Ttreintaysiete/ardcore/software/sketches/fac_drums_8552/pitch_table.c

#include "pitch_table.h"

PROGMEM prog_uint32_t pitch_table[2048] = {
	32768, 32812, 32857, 32901, 32946, 32991, 33035, 33080, 33125, 33170, 33215, 33260, 33305, 33350, 33395, 33440, 
	33486, 33531, 33576, 33622, 33667, 33713, 33759, 33804, 33850, 33896, 33942, 33988, 34034, 34080, 34126, 34172, 
	34219, 34265, 34312, 34358, 34405, 34451, 34498, 34545, 34591, 34638, 34685, 34732, 34779, 34826, 34874, 34921, 
	34968, 35015, 35063, 35110, 35158, 35206, 35253, 35301, 35349, 35397, 35445, 35493, 35541, 35589, 35637, 35685, 
	35734, 35782, 35831, 35879, 35928, 35976, 36025, 36074, 36123, 36172, 36221, 36270, 36319, 36368, 36417, 36467, 
	36516, 36566, 36615, 36665, 36715, 36764, 36814, 36864, 36914, 36964, 37014, 37064, 37114, 37165, 37215, 37265, 
	37316, 37366, 37417, 37468, 37518, 37569, 37620, 37671, 37722, 37773, 37824, 37876, 37927, 37978, 38030, 38081, 
	38133, 38185, 38236, 38288, 38340, 38392, 38444, 38496, 38548, 38600, 38653, 38705, 38757, 38810, 38863, 38915, 
	38968, 39021, 39074, 39127, 39180, 39233, 39286, 39339, 39392, 39446, 39499, 39553, 39606, 39660, 39714, 39767, 
	39821, 39875, 39929, 39983, 40037, 40092, 40146, 40200, 40255, 40309, 40364, 40419, 40473, 40528, 40583, 40638, 
	40693, 40748, 40804, 40859, 40914, 40970, 41025, 41081, 41136, 41192, 41248, 41304, 41360, 41416, 41472, 41528, 
	41584, 41641, 41697, 41753, 41810, 41867, 41923, 41980, 42037, 42094, 42151, 42208, 42265, 42323, 42380, 42437, 
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
	74632, 74733, 74834, 74935, 75037, 75139, 75240, 75342, 75444, 75547, 75649, 75751, 75854, 75957, 76060, 76163, 
	76266, 76369, 76473, 76576, 76680, 76784, 76888, 76992, 77096, 77201, 77305, 77410, 77515, 77620, 77725, 77830, 
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
};
