Ttreintaysiete/ardcore/software/sketches/fac_drums_8552/sample0.c

#include "sample0.h"

prog_uchar sample0_data[sample0_size] = {
	134, 122, 175, 216, 53, 137, 172, 89, 180, 91, 102, 141, 160, 138, 86, 157, 
	101, 152, 125, 105, 200, 39, 177, 182, 2, 158, 191, 171, 97, 120, 173, 78, 
	101, 140, 58, 129, 231, 158, 38, 151, 216, 29, 86, 255, 71, 95, 161, 104, 
	142, 161, 122, 110, 142, 107, 117, 114, 160, 67, 141, 181, 83, 135, 162, 109, 
	37, 181, 222, 57, 141, 126, 115, 151, 170, 93, 125, 150, 78, 179, 108, 161, 
	114, 114, 158, 153, 139, 99, 146, 118, 160, 86, 146, 144, 132, 158, 114, 126, 
	125, 113, 124, 163, 98, 163, 120, 89, 139, 130, 150, 83, 194, 96, 163, 72, 
	149, 154, 106, 155, 90, 164, 113, 135, 144, 84, 173, 107, 111, 126, 145, 118, 
	128, 145, 136, 131, 117, 136, 133, 129, 120, 134, 111, 156, 128, 142, 102, 128, 
	115, 125, 139, 134, 163, 101, 135, 119, 156, 112, 120, 101, 167, 132, 129, 150, 
	87, 167, 101, 120, 155, 130, 105, 154, 130, 112, 148, 118, 118, 110, 172, 103, 
	149, 148, 99, 132, 113, 135, 121, 115, 138, 128, 140, 138, 88, 140, 159, 117, 
	105, 160, 130, 137, 102, 121, 176, 121, 128, 104, 148, 143, 114, 106, 166, 107, 
	164, 134, 84, 153, 136, 123, 162, 98, 129, 139, 135, 130, 119, 146, 137, 131, 
	90, 162, 118, 139, 113, 129, 134, 113, 151, 125, 111, 142, 142, 142, 112, 128, 
	145, 152, 107, 109, 135, 161, 118, 141, 98, 139, 131, 136, 118, 104, 167, 112, 
	130, 118, 83, 202, 127, 98, 154, 116, 143, 107, 128, 153, 164, 71, 128, 163, 
	113, 117, 141, 120, 128, 139, 147, 80, 150, 146, 107, 143, 84, 153, 152, 123, 
	138, 136, 112, 117, 154, 124, 143, 136, 89, 176, 114, 87, 168, 137, 104, 134, 
	155, 103, 148, 125, 89, 161, 129, 101, 159, 122, 126, 137, 125, 135, 130, 136, 
	126, 119, 132, 137, 117, 128, 149, 116, 129, 160, 82, 175, 149, 94, 136, 148, 
	105, 137, 132, 122, 130, 136, 118, 126, 165, 91, 147, 134, 137, 131, 82, 172, 
	116, 147, 101, 162, 114, 134, 123, 128, 162, 106, 123, 129, 129, 166, 93, 109, 
	175, 92, 132, 152, 122, 129, 133, 135, 97, 155, 118, 139, 163, 62, 150, 134, 
	127, 139, 129, 128, 134, 98, 137, 167, 110, 139, 111, 123, 150, 132, 149, 95, 
	140, 128, 132, 124, 124, 162, 113, 121, 140, 132, 117, 136, 148, 114, 97, 168, 
	130, 138, 122, 132, 109, 137, 151, 80, 175, 112, 121, 148, 113, 155, 128, 117, 
	128, 130, 139, 109, 151, 128, 153, 94, 127, 149, 114, 157, 103, 152, 96, 132, 
	167, 93, 148, 119, 122, 158, 109, 128, 124, 172, 101, 126, 136, 110, 159, 134, 
	113, 100, 178, 126, 90, 178, 120, 109, 140, 114, 156, 136, 130, 122, 128, 147, 
	113, 138, 128, 143, 117, 130, 129, 119, 149, 110, 141, 128, 113, 136, 153, 126, 
	112, 131, 138, 120, 138, 138, 125, 122, 127, 124, 150, 126, 140, 108, 133, 129, 
	117, 143, 137, 114, 116, 167, 104, 123, 148, 121, 121, 131, 148, 117, 130, 117, 
	132, 162, 106, 108, 149, 131, 124, 125, 124, 129, 138, 131, 134, 133, 100, 140, 
	131, 148, 155, 94, 143, 134, 125, 133, 134, 120, 137, 109, 127, 153, 122, 113, 
	171, 80, 154, 126, 103, 143, 152, 115, 137, 115, 151, 117, 123, 138, 126, 151, 
	113, 124, 145, 139, 118, 127, 115, 150, 123, 139, 118, 135, 127, 133, 128, 132, 
	128, 135, 131, 109, 154, 116, 140, 125, 147, 83, 147, 120, 152, 108, 111, 141, 
	142, 128, 126, 123, 136, 134, 132, 110, 160, 132, 133, 116, 128, 137, 131, 146, 
	109, 141, 129, 118, 114, 147, 148, 125, 116, 133, 112, 145, 141, 140, 117, 94, 
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
};
