Ttreintaysiete/ardcore/software/sketches/fac_drums_8552/sample1.c

#include "sample1.h"

prog_uchar sample1_data[sample1_size] = {
	128, 132, 137, 110, 105, 174, 113, 117, 152, 100, 147, 127, 111, 162, 96, 142, 
	130, 119, 151, 124, 131, 118, 143, 144, 140, 125, 143, 158, 109, 129, 187, 125, 
	83, 157, 140, 121, 150, 171, 121, 149, 122, 133, 139, 129, 121, 80, 144, 91, 
	116, 130, 101, 118, 81, 143, 169, 77, 135, 124, 87, 134, 148, 83, 166, 108, 
	128, 202, 84, 122, 149, 151, 139, 119, 140, 172, 102, 179, 85, 150, 98, 174, 
	87, 141, 126, 132, 137, 122, 131, 134, 138, 106, 67, 175, 109, 149, 110, 112, 
	160, 102, 128, 116, 187, 105, 107, 211, 94, 151, 136, 173, 141, 98, 162, 151, 
	157, 164, 83, 181, 128, 103, 176, 80, 183, 96, 118, 165, 93, 134, 146, 125, 
	113, 106, 178, 61, 144, 91, 187, 146, 44, 224, 43, 163, 137, 100, 147, 90, 
	87, 160, 99, 142, 128, 95, 130, 71, 116, 216, 88, 100, 144, 68, 147, 104, 
	119, 119, 92, 186, 106, 114, 198, 71, 199, 132, 81, 231, 65, 225, 123, 140, 
	191, 71, 178, 108, 153, 185, 145, 113, 162, 65, 226, 110, 112, 123, 136, 141, 
	103, 151, 84, 146, 141, 97, 118, 95, 126, 124, 122, 121, 63, 149, 114, 119, 
	93, 177, 78, 145, 127, 75, 186, 31, 184, 92, 146, 162, 95, 193, 121, 112, 
	181, 130, 160, 126, 103, 227, 78, 179, 147, 97, 132, 151, 161, 119, 124, 108, 
	150, 162, 87, 140, 121, 145, 142, 92, 156, 111, 116, 149, 89, 95, 186, 81, 
	134, 124, 104, 182, 50, 198, 60, 167, 134, 107, 141, 135, 102, 131, 137, 148, 
	80, 166, 146, 129, 136, 143, 153, 129, 152, 151, 97, 125, 152, 111, 88, 196, 
	89, 79, 178, 67, 154, 180, 48, 170, 69, 164, 114, 92, 186, 41, 196, 109, 
	115, 205, 72, 151, 121, 113, 200, 63, 200, 125, 148, 109, 164, 128, 99, 186, 
	181, 116, 86, 166, 96, 140, 127, 122, 172, 61, 135, 166, 84, 116, 113, 104, 
	118, 128, 119, 123, 149, 127, 79, 198, 136, 117, 153, 125, 144, 146, 138, 83, 
	177, 126, 120, 178, 55, 141, 146, 80, 129, 148, 110, 112, 137, 132, 131, 115, 
	113, 125, 162, 101, 117, 161, 78, 221, 99, 135, 159, 100, 219, 87, 176, 140, 
	56, 216, 123, 105, 200, 94, 138, 171, 79, 194, 100, 148, 132, 95, 148, 141, 
	82, 147, 92, 107, 152, 79, 158, 60, 137, 157, 42, 170, 96, 141, 124, 133, 
	156, 120, 102, 157, 112, 132, 143, 148, 145, 149, 128, 152, 112, 172, 128, 69, 
	255, 22, 172, 130, 162, 108, 128, 128, 106, 155, 104, 119, 165, 65, 132, 152, 
	106, 124, 151, 168, 39, 178, 85, 155, 150, 118, 69, 187, 96, 162, 150, 89, 
	131, 135, 136, 134, 125, 115, 140, 108, 154, 115, 142, 128, 94, 212, 43, 153, 
	170, 78, 219, 40, 216, 124, 101, 183, 84, 153, 134, 120, 138, 106, 137, 150, 
	88, 179, 149, 85, 204, 76, 126, 152, 140, 127, 104, 126, 121, 143, 134, 107, 
	153, 115, 112, 164, 86, 111, 133, 128, 111, 137, 159, 81, 155, 139, 92, 172, 
	105, 127, 163, 97, 154, 164, 116, 146, 135, 124, 204, 80, 151, 159, 76, 215, 
	80, 135, 151, 88, 166, 101, 119, 141, 109, 173, 82, 133, 131, 110, 129, 117, 
	120, 147, 117, 128, 108, 129, 142, 113, 123, 135, 131, 132, 156, 100, 153, 106, 
	119, 149, 133, 138, 153, 120, 165, 136, 137, 124, 119, 171, 152, 98, 141, 146, 
	122, 130, 149, 116, 138, 120, 145, 95, 120, 151, 98, 123, 121, 118, 142, 115, 
	116, 132, 101, 160, 73, 169, 118, 59, 201, 123, 101, 158, 128, 168, 97, 175, 
	104, 147, 123, 128, 164, 109, 136, 156, 117, 138, 110, 186, 115, 118, 132, 117, 
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
};
