Ttreintaysiete/ardcore/software/sketches/fac_drums_8552/sample2.c

#include "sample2.h"

prog_uchar sample2_data[sample2_size] = {
	129, 128, 124, 126, 124, 124, 124, 123, 114, 104, 98, 108, 86, 91, 92, 68, 
	67, 27, 39, 87, 115, 79, 49, 49, 90, 96, 79, 84, 108, 75, 112, 110, 
	101, 132, 123, 129, 147, 155, 138, 171, 179, 157, 187, 192, 200, 193, 207, 231, 
	213, 250, 232, 246, 252, 245, 251, 248, 252, 251, 252, 252, 253, 252, 253, 252, 
	254, 253, 255, 253, 255, 254, 255, 254, 249, 250, 249, 232, 230, 234, 208, 220, 
	198, 203, 181, 182, 167, 156, 161, 129, 134, 119, 118, 90, 98, 94, 59, 54, 
	65, 51, 26, 32, 27, 18, 18, 21, 19, 19, 18, 17, 17, 17, 16, 16, 
	16, 15, 15, 16, 14, 15, 14, 14, 13, 13, 12, 14, 11, 12, 11, 12, 
	10, 10, 10, 10, 9, 9, 8, 9, 8, 7, 8, 7, 8, 14, 17, 36, 
	39, 39, 71, 58, 70, 99, 81, 128, 97, 135, 151, 134, 161, 172, 174, 183, 
	201, 197, 214, 214, 234, 226, 236, 239, 235, 237, 236, 238, 237, 239, 237, 239, 
	239, 239, 239, 239, 240, 241, 240, 241, 240, 242, 241, 241, 243, 243, 242, 244, 
	242, 245, 243, 245, 244, 246, 245, 245, 247, 246, 247, 245, 241, 239, 231, 218, 
	211, 215, 191, 193, 183, 171, 170, 144, 159, 145, 125, 122, 124, 109, 97, 100, 
	91, 76, 79, 57, 72, 55, 38, 58, 32, 33, 38, 20, 34, 21, 21, 23, 
	23, 20, 23, 20, 22, 20, 21, 20, 20, 19, 20, 19, 18, 19, 19, 17, 
	18, 18, 17, 17, 17, 15, 17, 15, 15, 16, 15, 14, 15, 13, 15, 12, 
	16, 26, 22, 26, 37, 31, 41, 50, 35, 60, 51, 66, 63, 70, 76, 82, 
	82, 89, 106, 95, 101, 126, 118, 128, 133, 133, 155, 142, 165, 158, 178, 173, 
	180, 190, 194, 198, 204, 210, 211, 221, 225, 225, 223, 226, 226, 227, 225, 228, 
	227, 227, 228, 229, 228, 228, 230, 228, 230, 230, 230, 231, 231, 230, 233, 231, 
	232, 232, 233, 233, 233, 233, 234, 234, 234, 235, 235, 236, 235, 236, 236, 237, 
	237, 236, 239, 236, 239, 238, 239, 239, 239, 239, 241, 232, 237, 232, 221, 230, 
	220, 213, 213, 212, 203, 200, 191, 194, 190, 178, 176, 178, 160, 166, 160, 148, 
	149, 145, 129, 135, 132, 122, 121, 120, 117, 113, 109, 105, 101, 94, 90, 85, 
	80, 74, 71, 64, 62, 55, 52, 48, 46, 42, 42, 40, 40, 39, 39, 39, 
	38, 39, 39, 38, 37, 38, 38, 36, 37, 36, 36, 35, 36, 35, 34, 35, 
	34, 33, 34, 33, 32, 33, 31, 31, 33, 29, 31, 30, 30, 29, 30, 28, 
	29, 28, 28, 27, 28, 26, 28, 37, 48, 46, 48, 46, 46, 46, 47, 47, 
	46, 49, 49, 51, 55, 56, 58, 61, 64, 66, 68, 70, 74, 75, 78, 80, 
	83, 85, 89, 89, 94, 94, 98, 101, 103, 105, 108, 111, 113, 115, 118, 121, 
	123, 126, 128, 130, 132, 136, 137, 139, 144, 144, 148, 149, 154, 154, 158, 159, 
	162, 165, 166, 168, 172, 173, 176, 178, 180, 182, 185, 186, 189, 190, 193, 195, 
	195, 199, 199, 200, 202, 200, 203, 202, 202, 203, 203, 204, 203, 204, 204, 205, 
	204, 205, 206, 206, 205, 208, 206, 207, 208, 208, 207, 209, 209, 209, 210, 209, 
	210, 210, 211, 211, 211, 213, 211, 212, 213, 213, 213, 214, 213, 214, 215, 214, 
	215, 215, 216, 216, 216, 216, 216, 217, 216, 218, 215, 217, 214, 213, 212, 211, 
	208, 206, 205, 203, 201, 198, 197, 193, 192, 190, 187, 185, 181, 181, 176, 175, 
	172, 170, 166, 165, 161, 159, 156, 155, 149, 149, 145, 143, 140, 138, 135, 131, 
	131, 127, 126, 121, 120, 118, 114, 113, 110, 108, 106, 102, 102, 97, 97, 95, 
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
};
