Ttreintaysiete/ardcore/software/sketches/fac_drums_8552/sample3.c

#include "sample3.h"

prog_uchar sample3_data[sample3_size] = {
	128, 123, 85, 126, 147, 103, 193, 103, 102, 70, 88, 121, 165, 128, 114, 126, 
	58, 128, 134, 78, 163, 149, 20, 91, 79, 52, 70, 40, 91, 94, 67, 79, 
	130, 135, 90, 91, 92, 96, 75, 66, 79, 45, 67, 53, 28, 85, 114, 75, 
	79, 88, 83, 91, 119, 128, 118, 92, 83, 75, 58, 97, 128, 137, 104, 92, 
	73, 78, 106, 137, 170, 145, 59, 103, 160, 195, 193, 174, 133, 103, 157, 196, 
	144, 128, 154, 138, 93, 101, 110, 136, 194, 230, 190, 128, 137, 154, 127, 150, 
	170, 166, 169, 176, 179, 175, 197, 244, 237, 180, 139, 157, 220, 255, 248, 231, 
	214, 189, 162, 152, 199, 248, 235, 227, 217, 203, 204, 201, 190, 176, 180, 184, 
	190, 205, 210, 220, 232, 224, 210, 194, 187, 192, 189, 191, 197, 189, 188, 206, 
	208, 213, 227, 212, 191, 176, 171, 172, 177, 176, 194, 205, 194, 175, 163, 164, 
	175, 175, 168, 160, 149, 135, 128, 134, 134, 137, 151, 149, 133, 149, 148, 120, 
	97, 108, 128, 141, 144, 145, 155, 147, 113, 76, 76, 89, 79, 64, 54, 56, 
	61, 64, 61, 49, 27, 38, 55, 59, 66, 63, 61, 66, 70, 64, 52, 46, 
	59, 67, 49, 38, 41, 50, 54, 56, 46, 21, 13, 31, 34, 21, 40, 41, 
	23, 15, 9, 9, 9, 12, 10, 13, 33, 48, 48, 42, 38, 38, 32, 29, 
	27, 43, 75, 85, 61, 67, 84, 66, 57, 83, 97, 98, 93, 83, 72, 53, 
	48, 66, 86, 85, 73, 64, 70, 82, 89, 94, 89, 82, 76, 79, 76, 71, 
	78, 84, 89, 90, 98, 104, 105, 102, 92, 85, 84, 90, 97, 95, 97, 95, 
	96, 102, 115, 115, 101, 100, 117, 108, 96, 100, 108, 107, 100, 95, 94, 89, 
	80, 73, 78, 91, 98, 92, 83, 77, 81, 83, 82, 69, 75, 97, 98, 75, 
	75, 91, 88, 76, 68, 72, 82, 93, 92, 77, 52, 41, 43, 51, 57, 57, 
	55, 52, 56, 62, 68, 61, 61, 71, 77, 70, 71, 76, 82, 84, 87, 87, 
	92, 92, 94, 97, 105, 110, 116, 117, 114, 109, 108, 113, 114, 102, 99, 108, 
	122, 126, 133, 139, 145, 147, 152, 153, 154, 145, 139, 137, 141, 148, 151, 154, 
	161, 169, 174, 164, 161, 175, 187, 182, 180, 184, 194, 201, 202, 206, 207, 214, 
	222, 224, 222, 218, 217, 218, 220, 220, 221, 214, 212, 221, 228, 226, 224, 233, 
	240, 243, 243, 241, 238, 238, 237, 236, 238, 238, 237, 237, 239, 240, 245, 246, 
	246, 243, 242, 246, 246, 246, 241, 238, 241, 239, 239, 234, 229, 226, 226, 229, 
	233, 233, 230, 228, 225, 224, 219, 215, 215, 222, 228, 216, 204, 206, 207, 207, 
	200, 196, 191, 189, 183, 180, 179, 178, 182, 182, 179, 176, 173, 171, 172, 170, 
	159, 150, 148, 150, 147, 137, 133, 129, 129, 128, 127, 123, 118, 116, 111, 108, 
	105, 102, 99, 97, 96, 96, 97, 92, 89, 86, 85, 83, 78, 73, 70, 68, 
	75, 78, 77, 71, 68, 69, 68, 69, 68, 70, 72, 69, 61, 52, 57, 64, 
	66, 59, 53, 52, 53, 54, 58, 58, 61, 59, 55, 53, 51, 50, 53, 52, 
	53, 49, 50, 58, 67, 69, 62, 62, 63, 65, 66, 64, 64, 62, 64, 64, 
	66, 69, 68, 71, 72, 71, 75, 73, 78, 75, 78, 78, 80, 79, 76, 75, 
	77, 78, 81, 83, 86, 91, 93, 96, 96, 96, 96, 95, 93, 91, 92, 98, 
	103, 101, 94, 88, 92, 97, 100, 101, 101, 99, 99, 101, 102, 106, 108, 110, 
	109, 108, 110, 113, 113, 108, 102, 102, 105, 110, 112, 111, 111, 113, 112, 116, 
	114, 117, 115, 117, 116, 119, 118, 118, 120, 118, 120, 120, 120, 119, 121, 123, 
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
};
