Ttreintaysiete/ardcore/software/sketches/fac_drums_8552/sample4.c

#include "sample4.h"

prog_uchar sample4_data[sample4_size] = {
	129, 127, 91, 88, 87, 90, 86, 84, 88, 99, 68, 66, 72, 94, 127, 57, 
	24, 126, 105, 31, 111, 156, 141, 165, 166, 55, 134, 127, 204, 187, 139, 169, 
	105, 157, 201, 189, 206, 255, 169, 70, 142, 232, 219, 218, 204, 149, 172, 235, 
	215, 73, 158, 245, 183, 163, 189, 190, 188, 216, 188, 57, 108, 103, 195, 225, 
	79, 99, 143, 111, 176, 204, 25, 72, 119, 203, 147, 2, 53, 118, 125, 121, 
	85, 101, 79, 50, 83, 94, 85, 148, 148, 2, 79, 201, 70, 24, 110, 113, 
	139, 108, 41, 80, 104, 109, 106, 102, 103, 127, 85, 99, 105, 119, 127, 211, 
	99, 28, 85, 137, 198, 137, 117, 136, 143, 146, 133, 155, 162, 109, 139, 162, 
	237, 142, 29, 95, 195, 205, 213, 225, 107, 97, 185, 198, 140, 158, 193, 210, 
	131, 164, 183, 250, 129, 140, 165, 100, 129, 196, 196, 205, 147, 139, 156, 166, 
	154, 135, 133, 160, 150, 101, 127, 180, 162, 23, 123, 140, 135, 142, 116, 22, 
	65, 123, 137, 115, 110, 105, 90, 62, 138, 88, 48, 79, 167, 59, 99, 84, 
	37, 137, 154, 45, 138, 65, 45, 124, 101, 115, 118, 114, 154, 96, 101, 78, 
	133, 153, 36, 114, 144, 161, 139, 137, 131, 135, 152, 173, 93, 110, 159, 143, 
	144, 156, 174, 205, 58, 117, 154, 223, 193, 116, 93, 113, 182, 201, 158, 163, 
	226, 126, 105, 133, 135, 184, 203, 191, 114, 174, 143, 109, 162, 170, 165, 150, 
	147, 135, 153, 149, 182, 112, 83, 132, 187, 151, 97, 98, 83, 154, 138, 118, 
	120, 136, 111, 99, 114, 137, 91, 59, 94, 119, 101, 117, 141, 96, 69, 47, 
	90, 127, 126, 102, 102, 103, 90, 110, 86, 112, 120, 141, 84, 34, 114, 129, 
	132, 123, 121, 119, 137, 106, 118, 122, 123, 147, 168, 145, 53, 105, 165, 203, 
	151, 66, 130, 162, 174, 174, 189, 119, 127, 130, 126, 165, 169, 176, 185, 101, 
	129, 167, 164, 200, 189, 96, 114, 174, 145, 121, 171, 168, 161, 161, 134, 126, 
	154, 164, 161, 126, 86, 142, 138, 152, 142, 138, 138, 174, 84, 140, 91, 92, 
	148, 154, 129, 121, 72, 84, 120, 164, 136, 93, 106, 88, 112, 124, 127, 64, 
	110, 115, 117, 119, 154, 70, 63, 104, 159, 74, 98, 114, 132, 104, 133, 123, 
	78, 89, 150, 111, 139, 98, 83, 120, 160, 140, 139, 130, 71, 116, 171, 166, 
	100, 128, 141, 151, 162, 123, 147, 168, 93, 141, 153, 186, 129, 131, 147, 159, 
	157, 191, 131, 100, 189, 129, 113, 178, 166, 127, 152, 153, 160, 177, 113, 153, 
	147, 99, 128, 156, 164, 145, 133, 131, 133, 136, 133, 136, 136, 120, 144, 155, 
	68, 98, 134, 143, 127, 147, 151, 57, 95, 126, 134, 128, 118, 143, 79, 89, 
	122, 131, 104, 130, 109, 92, 99, 113, 132, 110, 115, 128, 125, 85, 103, 96, 
	106, 133, 130, 139, 110, 105, 134, 151, 73, 124, 153, 104, 101, 136, 138, 172, 
	128, 89, 125, 148, 150, 155, 118, 110, 142, 150, 144, 136, 139, 141, 141, 142, 
	139, 173, 145, 89, 129, 152, 157, 149, 145, 141, 143, 142, 173, 120, 106, 146, 
	146, 157, 143, 138, 132, 127, 130, 164, 131, 109, 154, 109, 125, 138, 141, 136, 
	160, 105, 94, 130, 133, 143, 122, 134, 116, 121, 99, 113, 139, 148, 96, 117, 
	127, 114, 111, 109, 126, 127, 127, 117, 114, 140, 120, 95, 99, 125, 139, 99, 
	131, 121, 129, 136, 95, 107, 128, 153, 121, 96, 128, 129, 132, 126, 133, 123, 
	151, 129, 95, 128, 138, 140, 136, 134, 133, 138, 133, 133, 133, 143, 158, 110, 
	122, 140, 155, 140, 134, 142, 137, 141, 154, 156, 107, 148, 135, 130, 151, 128, 
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
};
