Ttreintaysiete/ardcore/software/sketches/fac_drums_8552/sample5.c

#include "sample5.h"

prog_uchar sample5_data[sample5_size] = {
	127, 135, 141, 129, 77, 230, 205, 164, 182, 155, 219, 187, 166, 194, 165, 152, 
	185, 158, 155, 160, 140, 151, 117, 137, 120, 51, 122, 100, 46, 67, 44, 42, 
	21, 29, 21, 18, 12, 48, 19, 32, 75, 2, 64, 77, 23, 63, 70, 91, 
	89, 80, 118, 123, 112, 121, 194, 139, 143, 199, 201, 167, 238, 184, 193, 245, 
	208, 212, 187, 254, 193, 217, 207, 205, 239, 153, 180, 211, 142, 145, 150, 166, 
	124, 136, 133, 102, 94, 115, 86, 131, 57, 74, 142, 56, 115, 83, 61, 145, 
	66, 89, 31, 120, 107, 71, 120, 56, 97, 96, 61, 116, 67, 117, 121, 71, 
	88, 91, 110, 98, 84, 96, 121, 62, 123, 113, 83, 145, 98, 117, 134, 117, 
	128, 139, 146, 152, 107, 165, 165, 150, 175, 127, 214, 159, 141, 196, 163, 150, 
	216, 160, 163, 190, 195, 192, 216, 205, 166, 217, 231, 190, 225, 247, 239, 198, 
	255, 231, 226, 223, 209, 248, 219, 201, 236, 230, 186, 218, 187, 198, 205, 175, 
	171, 171, 173, 173, 125, 155, 163, 118, 127, 91, 157, 125, 92, 102, 101, 118, 
	75, 84, 98, 60, 51, 86, 48, 78, 31, 32, 89, 28, 35, 61, 39, 42, 
	22, 78, 16, 68, 40, 49, 49, 81, 49, 70, 77, 85, 86, 84, 94, 97, 
	108, 104, 113, 112, 119, 132, 123, 143, 145, 175, 143, 201, 176, 160, 206, 186, 
	215, 173, 210, 224, 189, 235, 184, 199, 239, 171, 231, 228, 186, 201, 203, 204, 
	178, 210, 205, 153, 195, 182, 159, 171, 141, 158, 178, 145, 141, 137, 142, 146, 
	96, 116, 163, 91, 121, 128, 94, 87, 123, 75, 110, 67, 79, 104, 41, 98, 
	71, 42, 57, 91, 67, 44, 53, 92, 71, 48, 67, 50, 79, 59, 63, 61, 
	65, 67, 55, 60, 87, 88, 48, 74, 136, 47, 89, 128, 54, 115, 90, 129, 
	110, 114, 113, 117, 136, 110, 140, 135, 145, 169, 139, 155, 147, 167, 190, 136, 
	193, 201, 196, 159, 161, 213, 232, 162, 216, 220, 163, 213, 202, 229, 176, 197, 
	235, 187, 138, 195, 225, 151, 183, 223, 145, 191, 221, 128, 214, 195, 102, 187, 
	149, 158, 148, 116, 167, 109, 112, 142, 48, 131, 97, 113, 126, 90, 74, 93, 
	98, 89, 86, 119, 84, 87, 99, 91, 84, 53, 99, 112, 91, 43, 108, 102, 
	101, 84, 93, 66, 107, 75, 121, 119, 47, 112, 112, 76, 119, 79, 79, 123, 
	92, 115, 85, 97, 124, 61, 86, 134, 82, 76, 98, 149, 65, 113, 121, 96, 
	67, 99, 132, 84, 126, 88, 104, 159, 77, 97, 153, 92, 119, 111, 123, 128, 
	109, 163, 132, 111, 154, 114, 127, 163, 129, 156, 147, 133, 114, 174, 149, 155, 
	128, 159, 184, 130, 144, 152, 144, 158, 135, 153, 178, 133, 172, 171, 130, 190, 
	160, 170, 159, 150, 160, 178, 167, 150, 207, 142, 163, 203, 139, 178, 191, 130, 
	178, 167, 157, 183, 149, 147, 168, 160, 138, 151, 152, 131, 150, 142, 127, 131, 
	142, 139, 101, 128, 118, 117, 135, 95, 106, 117, 122, 67, 96, 151, 60, 124, 
	121, 64, 112, 75, 96, 101, 93, 103, 75, 95, 84, 88, 81, 78, 92, 61, 
	79, 82, 76, 78, 67, 113, 75, 48, 128, 70, 81, 107, 72, 112, 62, 108, 
	112, 77, 99, 101, 117, 130, 107, 106, 119, 143, 104, 138, 152, 115, 138, 136, 
	142, 147, 128, 165, 167, 156, 172, 159, 177, 181, 155, 188, 183, 169, 179, 184, 
	182, 183, 190, 167, 210, 162, 181, 205, 160, 179, 179, 165, 180, 163, 177, 178, 
	161, 166, 182, 148, 180, 156, 146, 160, 160, 134, 171, 141, 135, 165, 128, 138, 
	135, 110, 141, 125, 133, 131, 120, 139, 124, 102, 116, 124, 118, 99, 135, 97, 
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
};
