Ttreintaysiete/ardcore/software/sketches/fac_drums_8552/sample6.c

#include "sample6.h"

prog_uchar sample6_data[sample6_size] = {
	128, 133, 133, 137, 37, 41, 202, 223, 115, 64, 113, 215, 147, 35, 49, 149, 
	208, 93, 43, 128, 149, 82, 157, 207, 165, 90, 55, 34, 75, 156, 194, 145, 
	96, 203, 224, 235, 207, 148, 39, 31, 199, 215, 45, 50, 57, 101, 203, 174, 
	165, 174, 158, 188, 250, 233, 234, 241, 240, 185, 61, 11, 13, 17, 33, 22, 
	36, 138, 173, 204, 235, 156, 194, 151, 110, 70, 61, 96, 118, 145, 124, 121, 
	84, 86, 178, 160, 70, 76, 181, 244, 235, 138, 65, 116, 180, 175, 76, 29, 
	25, 19, 22, 21, 68, 160, 186, 202, 238, 206, 144, 160, 246, 229, 228, 146, 
	87, 101, 84, 140, 152, 90, 14, 25, 54, 58, 65, 95, 142, 204, 226, 203, 
	174, 168, 188, 189, 187, 174, 118, 71, 70, 136, 161, 116, 54, 38, 72, 104, 
	134, 134, 169, 196, 173, 165, 168, 171, 154, 96, 74, 102, 152, 134, 58, 63, 
	109, 128, 122, 137, 169, 170, 158, 128, 134, 186, 229, 202, 140, 131, 153, 169, 
	149, 103, 98, 95, 71, 75, 94, 100, 120, 164, 182, 165, 134, 87, 60, 59, 
	81, 103, 118, 92, 82, 106, 128, 165, 173, 173, 181, 177, 160, 162, 159, 157, 
	166, 149, 116, 94, 74, 35, 37, 59, 89, 143, 135, 135, 128, 90, 89, 94, 
	117, 151, 168, 162, 147, 147, 135, 146, 185, 197, 163, 153, 133, 111, 111, 123, 
	152, 166, 131, 91, 84, 102, 106, 124, 147, 163, 144, 114, 123, 141, 158, 169, 
	168, 137, 116, 115, 87, 85, 112, 155, 163, 151, 137, 123, 127, 127, 153, 155, 
	133, 115, 130, 121, 106, 100, 96, 114, 116, 102, 79, 73, 91, 134, 170, 161, 
	184, 188, 128, 120, 128, 137, 144, 147, 124, 115, 131, 118, 93, 93, 114, 132, 
	114, 95, 96, 123, 184, 202, 193, 174, 120, 119, 133, 106, 86, 88, 117, 150, 
	136, 113, 112, 127, 156, 171, 202, 186, 152, 139, 120, 132, 155, 183, 152, 107, 
	102, 87, 68, 72, 78, 79, 125, 145, 122, 116, 134, 168, 163, 135, 141, 154, 
	148, 115, 120, 117, 100, 131, 133, 110, 99, 111, 111, 118, 142, 153, 144, 128, 
	135, 169, 152, 136, 145, 130, 126, 129, 105, 88, 115, 130, 130, 127, 116, 105, 
	123, 144, 165, 169, 140, 142, 160, 168, 135, 104, 94, 106, 127, 102, 95, 114, 
	118, 111, 146, 166, 134, 123, 119, 133, 150, 144, 137, 136, 133, 135, 144, 121, 
	90, 116, 118, 122, 138, 147, 136, 134, 144, 152, 146, 148, 128, 105, 114, 123, 
	96, 86, 130, 149, 156, 141, 111, 103, 108, 132, 151, 153, 135, 149, 171, 160, 
	136, 129, 158, 165, 155, 125, 106, 93, 87, 119, 139, 122, 86, 69, 134, 179, 
	131, 112, 122, 123, 122, 110, 118, 128, 126, 104, 120, 151, 123, 97, 131, 157, 
	172, 139, 112, 130, 144, 140, 135, 148, 148, 132, 124, 161, 165, 152, 121, 86, 
	101, 110, 109, 93, 90, 132, 146, 140, 131, 125, 120, 140, 153, 166, 162, 171, 
	155, 129, 127, 124, 127, 108, 99, 96, 111, 130, 129, 126, 137, 132, 128, 131, 
	147, 138, 128, 139, 152, 151, 116, 132, 136, 105, 113, 128, 130, 112, 128, 134, 
	133, 132, 136, 131, 127, 126, 140, 128, 115, 122, 118, 116, 109, 115, 125, 133, 
	120, 117, 131, 124, 126, 141, 137, 141, 133, 136, 138, 138, 146, 146, 140, 117, 
	131, 148, 134, 125, 110, 105, 105, 108, 123, 146, 144, 132, 154, 149, 126, 124, 
	123, 139, 140, 121, 104, 120, 116, 122, 153, 147, 143, 127, 115, 143, 152, 147, 
	127, 122, 153, 150, 139, 135, 121, 95, 109, 109, 123, 125, 107, 129, 141, 132, 
	133, 132, 138, 138, 128, 131, 136, 127, 130, 142, 130, 103, 122, 143, 133, 128, 
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
};
