Ttreintaysiete/ardcore/software/sketches/fac_drums_8552/sample7.c

#include "sample7.h"

prog_uchar sample7_data[sample7_size] = {
	129, 128, 118, 116, 112, 110, 108, 115, 133, 133, 134, 136, 140, 142, 144, 144, 
	145, 146, 145, 143, 167, 203, 184, 155, 136, 121, 104, 95, 86, 81, 80, 78, 
	84, 89, 98, 109, 109, 147, 201, 196, 185, 183, 175, 166, 146, 128, 115, 104, 
	94, 88, 86, 87, 90, 85, 85, 89, 98, 107, 121, 131, 145, 156, 168, 180, 
	182, 188, 239, 253, 246, 247, 215, 176, 144, 117, 87, 61, 43, 30, 19, 12, 
	12, 19, 30, 41, 52, 68, 89, 115, 136, 155, 168, 185, 199, 208, 219, 224, 
	228, 223, 239, 251, 228, 197, 174, 150, 124, 98, 76, 59, 43, 35, 32, 57, 
	84, 73, 65, 65, 76, 82, 96, 109, 125, 138, 152, 165, 177, 186, 192, 190, 
	217, 234, 217, 199, 182, 163, 141, 115, 95, 76, 63, 55, 47, 49, 53, 60, 
	62, 73, 85, 101, 117, 135, 152, 168, 181, 194, 202, 205, 216, 247, 238, 233, 
	225, 191, 157, 131, 106, 80, 60, 41, 32, 21, 21, 25, 33, 44, 56, 69, 
	85, 106, 126, 146, 160, 173, 187, 197, 206, 210, 213, 212, 208, 220, 221, 196, 
	171, 153, 132, 112, 94, 78, 64, 55, 51, 53, 77, 89, 84, 79, 85, 93, 
	102, 113, 125, 136, 146, 157, 164, 174, 177, 180, 180, 197, 203, 190, 174, 159, 
	146, 128, 110, 96, 84, 75, 71, 66, 70, 74, 79, 83, 91, 103, 114, 128, 
	138, 152, 164, 172, 180, 186, 187, 201, 217, 204, 202, 193, 164, 143, 125, 105, 
	89, 74, 63, 55, 52, 50, 55, 62, 71, 80, 88, 103, 118, 132, 145, 154, 
	165, 173, 181, 186, 188, 190, 187, 185, 197, 192, 171, 156, 142, 128, 113, 100, 
	90, 81, 74, 73, 79, 94, 103, 94, 94, 99, 105, 111, 120, 128, 135, 144, 
	150, 156, 162, 165, 164, 168, 179, 182, 170, 159, 149, 140, 126, 113, 104, 95, 
	89, 86, 85, 86, 90, 95, 97, 104, 112, 120, 130, 138, 147, 156, 161, 166, 
	171, 172, 186, 192, 181, 184, 171, 150, 137, 124, 109, 97, 88, 79, 75, 73, 
	72, 76, 83, 87, 96, 102, 111, 125, 132, 142, 149, 155, 163, 166, 171, 172, 
	174, 170, 172, 180, 172, 157, 148, 136, 128, 116, 107, 100, 92, 90, 89, 95, 
	107, 109, 103, 103, 107, 112, 117, 123, 128, 135, 140, 145, 150, 153, 156, 155, 
	159, 169, 167, 159, 149, 145, 135, 125, 117, 109, 103, 100, 96, 98, 97, 102, 
	104, 106, 112, 117, 124, 131, 137, 144, 149, 154, 158, 160, 163, 176, 173, 168, 
	170, 157, 141, 134, 122, 113, 104, 96, 91, 88, 86, 88, 91, 94, 100, 105, 
	110, 118, 127, 133, 140, 144, 150, 154, 159, 162, 161, 163, 161, 162, 168, 159, 
	150, 141, 134, 126, 119, 111, 110, 107, 105, 105, 112, 116, 117, 113, 113, 117, 
	119, 122, 126, 129, 133, 136, 140, 141, 145, 145, 145, 149, 154, 152, 147, 142, 
	138, 131, 126, 120, 117, 112, 111, 109, 109, 111, 112, 114, 115, 119, 122, 128, 
	130, 136, 138, 143, 145, 147, 149, 154, 159, 156, 154, 155, 143, 137, 131, 123, 
	118, 113, 107, 104, 104, 102, 103, 105, 109, 110, 115, 118, 123, 128, 133, 136, 
	139, 144, 145, 149, 149, 151, 151, 149, 153, 153, 148, 141, 138, 131, 126, 122, 
	118, 113, 111, 109, 112, 115, 120, 117, 115, 117, 119, 121, 124, 126, 130, 132, 
	135, 138, 140, 142, 143, 143, 146, 150, 149, 143, 139, 137, 129, 127, 120, 119, 
	115, 114, 111, 114, 113, 115, 117, 118, 121, 124, 128, 131, 135, 137, 141, 143, 
	144, 147, 152, 153, 150, 151, 149, 141, 134, 130, 124, 118, 114, 111, 108, 106, 
	107, 107, 109, 113, 113, 118, 120, 126, 128, 133, 136, 137, 142, 144, 146, 146, 
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
};
